SW-Corp/electronics/STL/BMP280/BMP280-BOX-BODY-V2.stl

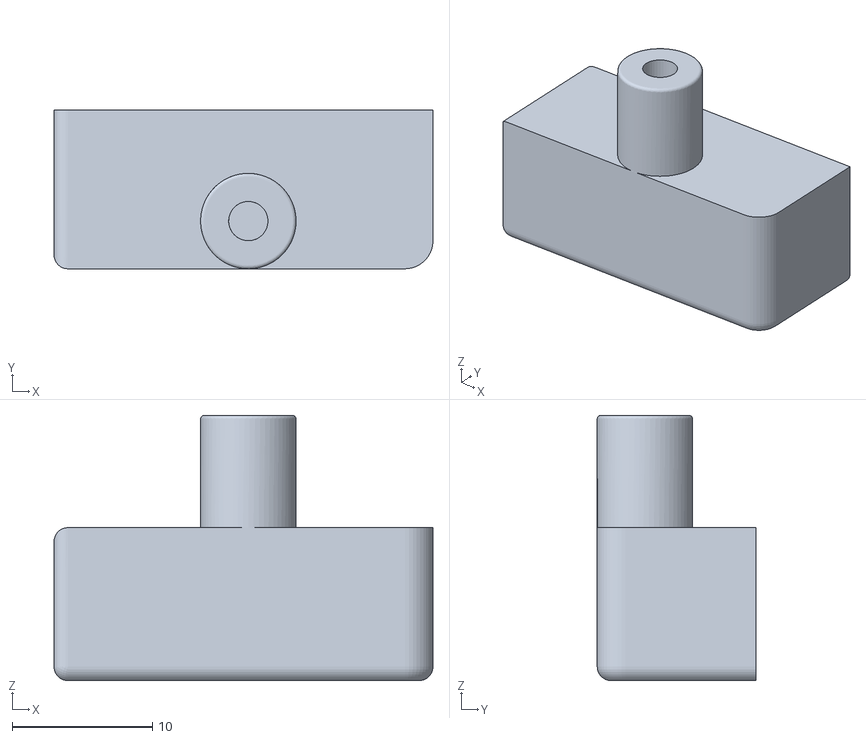
[picture p15: CAD file, 2022-09-18]
STL/BMP280/BMP280-BOX-BODY-V2.stl
27.0 x 11.3 x 18.9
