SW-Corp/electronics/STL/BMPCase/Cover.stl

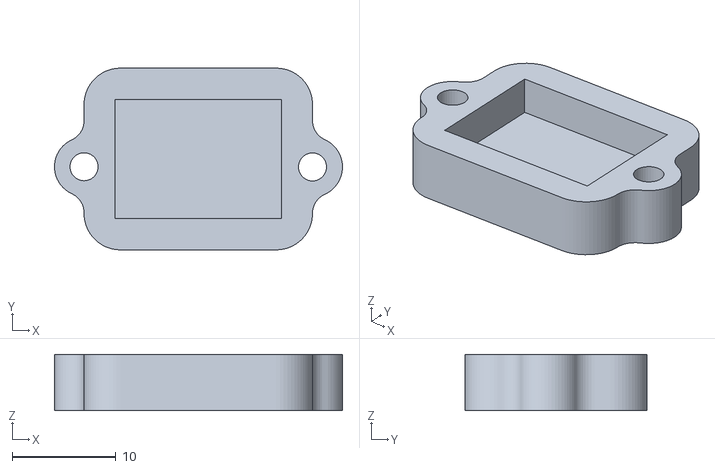
[picture p16: CAD file, 2022-09-18]
STL/BMPCase/Cover.stl
27.7 x 17.5 x 5.40
