SW-Corp/electronics/STL/PowerAdapter/Body.stl

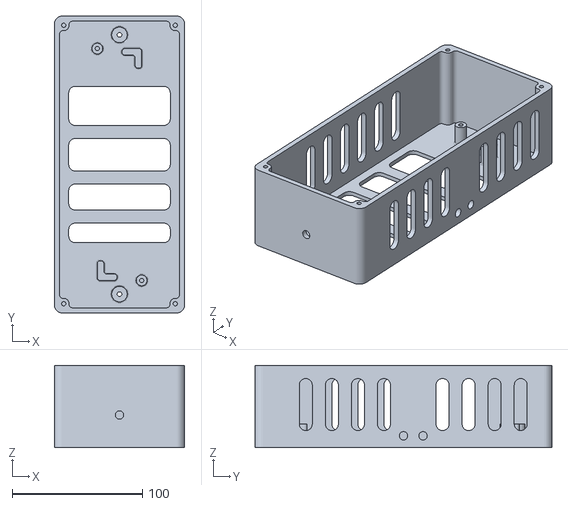
[picture p17: CAD file, 2022-09-18]
STL/PowerAdapter/Body.stl
100.0 x 228.0 x 63.0
