SW-Corp/electronics/STL/SwitchPlate/SwitchPlate_deep.stl

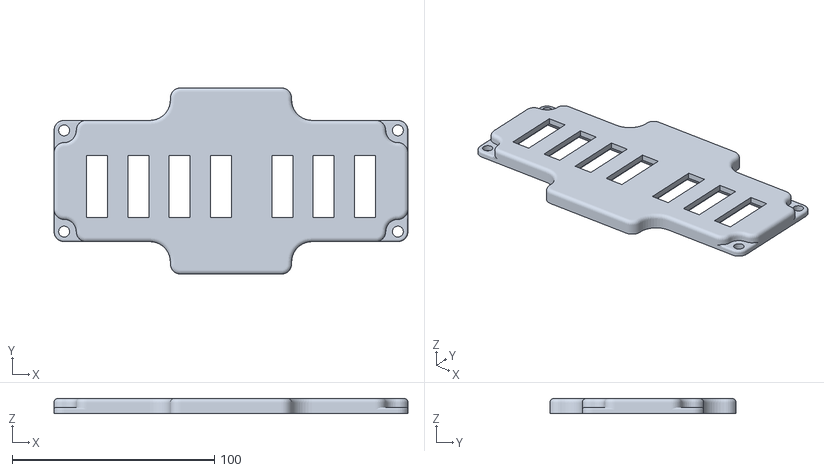
[picture p18: CAD file, 2022-09-18]
STL/SwitchPlate/SwitchPlate_deep.stl
175.0 x 92.0 x 7.50
