SW-Corp/electronics/STL/WaterPipeHolder/Big/Top.stl

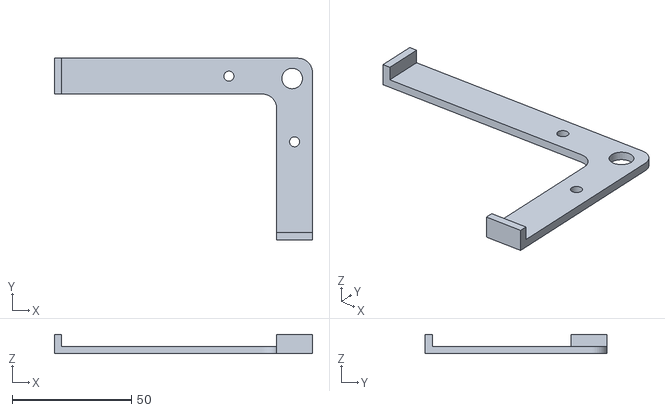
[picture p19: CAD file, 2022-09-18]
STL/WaterPipeHolder/Big/Top.stl
108.0 x 76.0 x 8.00
