SW-Corp/electronics/STL/WaterPipeHolder/Middle/Top.stl

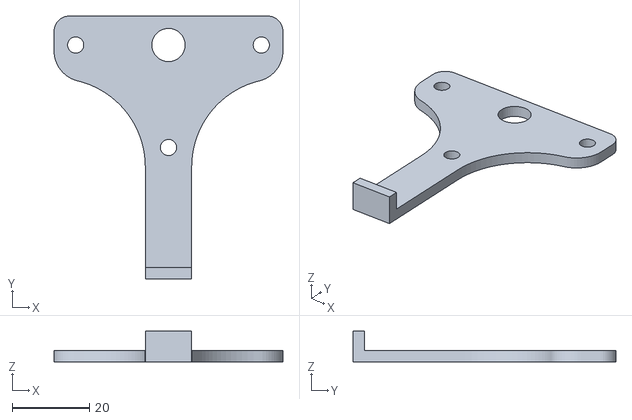
[picture p20: CAD file, 2022-09-18]
STL/WaterPipeHolder/Middle/Top.stl
59.2 x 68.0 x 8.00
