SW-Corp/electronics/STL/WaterPipeHolder/WithSensor/Bottom.stl

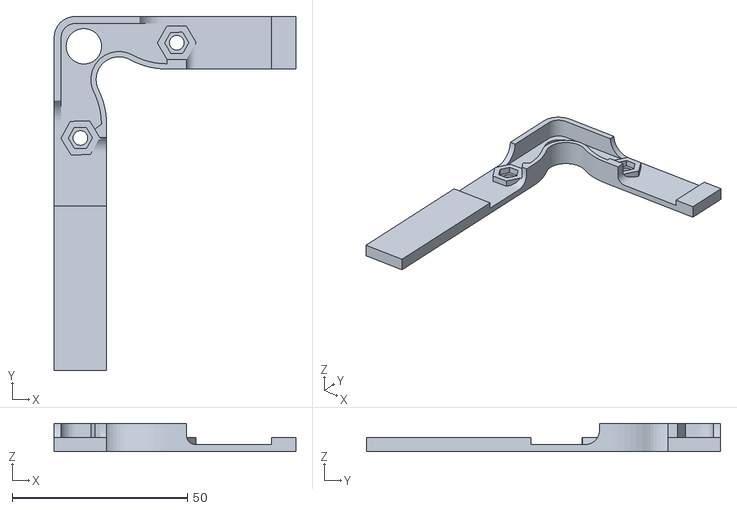
[picture p21: CAD file, 2022-09-18]
STL/WaterPipeHolder/WithSensor/Bottom.stl
69.0 x 101.0 x 8.00
