SW-Corp/electronics/STL/WaterPipeHolder/Middle/Mid.stl

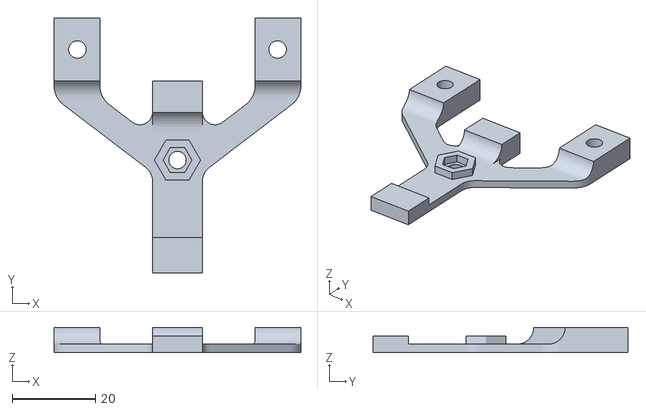
[picture p22: CAD file, 2022-09-18]
STL/WaterPipeHolder/Middle/Mid.stl
59.2 x 61.0 x 6.00
